giacomo-ascari/busy-toad/src/bt_h750/Drivers/CS4282P/Inc/cs4282p.h

#pragma once

#include "stm32h7xx_hal.h"
#include "stm32h7xx_hal_i2s.h"

//#define CS4282P_WRITE_ADDRESS 0x6E
//#define CS4282P_READ_ADDRESS  0x6F
#define CS4282P_I2C_ADDRESS (0x30U << 1) // 0x60

// DEVID
#define CS4282P_REG_DEVID 0x0000U 
#define CS4282P_REG_REVID 0x0004U
#define CS4282P_REG_SW_RESET 0x0022U
// CONFIG
#define CS4282P_REG_CLK_CFG_0 0x0040U
#define CS4282P_REG_CLK_CFG_1 0x0042U
#define CS4282P_REG_CHIP_ENABLE 0x0044U
#define CS4282P_REG_ASP_CFG 0x0048U
#define CS4282P_REG_SIGNAL_PATH_CFG 0x0050U
// INPUT_PATH
#define CS4282P_REG_IN_ENABLES 0x0080U
#define CS4282P_REG_IN_RAMP_SUM 0x0082U
#define CS4282P_REG_IN_FILTER 0x0086U
#define CS4282P_REG_IN_HIZ 0x0088U
#define CS4282P_REG_IN_INV 0x008AU
#define CS4282P_REG_IN_VOL_CTRL1_0 0x0090U
#define CS4282P_REG_IN_VOL_CTRL1_1 0x0092U
#define CS4282P_REG_IN_VOL_CTRL5 0x00A0U
// OUTPUT_PATH
#define CS4282P_REG_OUT_ENABLES 0x00C0U
#define CS4282P_REG_OUT_RAMP_SUM 0x00C2U
#define CS4282P_REG_OUT_DEEMPH 0x00C4U
#define CS4282P_REG_OUT_FILTER 0x00C6U
#define CS4282P_REG_OUT_INV 0x00CAU
#define CS4282P_REG_OUT_VOL_CTRL1_0 0x00D0U
#define CS4282P_REG_OUT_VOL_CTRL1_1 0x00D2U
#define CS4282P_REG_OUT_VOL_CTRL5 0x00E0U
#define CS4282P_REG_SHUTDOWN_CTRL 0x00E4U
#define CS4282P_REG_STARTUP_DELAY 0x00E6U
// CTRL_KEYS
#define CS4282P_REG_USER_KEY_CTRL 0x0104U
// HGC
#define CS4282P_REG_CONTROL 0x2000U
#define CS4282P_REG_STATUS 0x2004U
#define CS4282P_REG_GEN_CONFIG 0x2010U
#define CS4282P_REG_PATH_DELAY 0x2014U
#define CS4282P_REG_TM 0x2018U
#define CS4282P_REG_TM_LD_0 0x201CU
#define CS4282P_REG_TM_LD_1 0x201EU
#define CS4282P_REG_SPI_0 0x2020U
#define CS4282P_REG_SPI_1 0x2022U
#define CS4282P_REG_CH1_CONFIG 0x2030U
#define CS4282P_REG_CH2_CONFIG 0x2034U
#define CS4282P_REG_AUX1_CONFIG 0x2050U
#define CS4282P_REG_AUX2_CONFIG 0x2054U
#define CS4282P_REG_CH1_BIT_PATT_0 0x2060U
#define CS4282P_REG_CH1_BIT_PATT_1 0x2062U
#define CS4282P_REG_CH1_GAIN_0 0x2064U
#define CS4282P_REG_CH1_GAIN_1 0x2066U
#define CS4282P_REG_CH2_BIT_PATT_0 0x2068U
#define CS4282P_REG_CH2_BIT_PATT_1 0x206AU
#define CS4282P_REG_CH2_GAIN_0 0x206CU
#define CS4282P_REG_CH2_GAIN_1 0x206EU
#define CS4282P_REG_AUX1_BIT_PATT_0 0x20A0U
#define CS4282P_REG_AUX1_BIT_PATT_1 0x20A2U
#define CS4282P_REG_AUX2_BIT_PATT_0 0x20A4U
#define CS4282P_REG_AUX2_BIT_PATT_1 0x20A6U
// PIN_CONFIG
#define CS4282P_REG_PAD_DRV1_0 0x3D10U
#define CS4282P_REG_PAD_DRV1_1 0x3D12U
#define CS4282P_REG_PAD_DRV2_0 0x3D14U
#define CS4282P_REG_PAD_DRV2_1 0x3D16U
#define CS4282P_REG_PAD_CLIP 0x3D1CU
#define CS4282P_REG_PAD_HGC_SPI 0x3D20U
#define CS4282P_REG_PAD_FN 0x3D24U
#define CS4282P_REG_PAD_LVL 0x3D28U
// CLIP_DETECT
#define CS4282P_REG_CLIP_WARN 0x3E1CU
 
typedef struct {
    I2C_HandleTypeDef* hi2c;
    I2S_HandleTypeDef* hi2s;
    GPIO_TypeDef* resetPort;
    uint16_t resetPin;
    uint8_t initialized;
} CS4282P_HandleTypeDef;

uint8_t CS4282P_Init(CS4282P_HandleTypeDef* hcs4282p, I2C_HandleTypeDef* hi2c, I2S_HandleTypeDef* hi2s, GPIO_TypeDef* resetPort, uint16_t resetPin);
void CS4282P_Reset(CS4282P_HandleTypeDef* hcs4282p);
